NuclearInstruments/SingleEndedToDifferential/sim/ltspice_single_ended_to_fullydif.asc

C1: cap; 1.8p
C2: cap; 1.8p
R1: res; 1k
R2: res; 1k
R3: res; 1k
R4: res; 1k
U1: LTC6405
V1: signal; EXP(0 1 100n 10n 0 1u)
V2: battery; 5
V3: battery; 1
V4: battery; 1
Named nets: 0, +5V, +1V, +0.9V
.tran 4u
